fack07/OmegaSumo/firmware/Core/Src/main.c

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
/* Includes ------------------------------------------------------------------*/
#include "main.h"

/* USER CODE BEGIN Includes */
#include "stm32f4xx.h"
#include "system_stm32f4xx.h"
/* USER CODE END Includes */

TIM_HandleTypeDef htim1;
TIM_HandleTypeDef htim2;
TIM_HandleTypeDef htim4;
TIM_HandleTypeDef htim11;

/* USER CODE BEGIN PV */


#define NTRANS 27884	// Número de Transições
#define NESTADOS 2864	// Número de Estados
#define BUFFER 10	// Máximo Número de Eventos no Buffer

const unsigned int event[NTRANS]={0,4,7,8,9,11,13,15,17,18,19,0,1,4,7,8,9,11,13,15,17,18,19,8,9,11,13,15,16,17,18,19,1,8,9,11,13,15,16,17,18,19,8,9,11,13,15,16,17,18,19,
		1,8,9,11,13,15,16,17,18,19,0,4,7,8,9,11,13,15,17,18,19,22,0,1,4,7,8,9,11,13,15,17,18,19,22,8,9,11,13,15,17,18,19,22,1,8,9,11,13,15,17,
		18,19,22,8,9,11,13,15,17,18,19,22,1,8,9,11,13,15,17,18,19,22,8,9,11,13,15,17,18,19,22,1,8,9,11,13,15,17,18,19,22,8,9,11,13,15,17,18,19,22,1,
		8,9,11,13,15,17,18,19,22,2,4,7,8,9,11,14,15,17,18,19,4,7,8,9,11,14,15,17,18,19,1,2,4,7,8,9,11,14,15,17,18,19,1,4,7,8,9,11,14,15,17,
		18,19,8,9,11,14,15,16,17,18,19,1,8,9,11,14,15,16,17,18,19,8,9,11,14,15,16,17,18,19,1,8,9,11,14,15,16,17,18,19,2,4,7,8,9,11,14,15,17,18,19,
		22,4,7,8,9,11,14,15,17,18,19,22,1,2,4,7,8,9,11,14,15,17,18,19,22,1,4,7,8,9,11,14,15,17,18,19,22,8,9,11,14,15,17,18,19,22,1,8,9,11,14,
		15,17,18,19,22,8,9,11,14,15,17,18,19,22,1,8,9,11,14,15,17,18,19,22,8,9,11,14,15,17,18,19,22,1,8,9,11,14,15,17,18,19,22,8,9,11,14,15,17,18,19,
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
		2040,2041,0,2043,2044,2045,2046,2047,2048,2049,2050,0,2052,2053,2054,2055,2056,2057,2058,2059,2060,0,2062,2063,2064,2065,2066,2067,2068,2069,0,2071,2072,2073,2074,2075,2076,2077,2078,2079,0,2081,2082,2083,2084,2085,2086,2087,2088,2089,0,
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

/* USER CODE END PV */

void SystemClock_Config(void);
static void MX_GPIO_Init(void);
static void MX_TIM4_Init(void);
static void MX_TIM11_Init(void);
static void MX_TIM1_Init(void);
static void MX_TIM2_Init(void);
/* USER CODE BEGIN 0 */
// Mapeamento de eventos não controláveis como entradas
#define p1a 8	// Entrada 0
#define p2a 9	// Entrada 1
#define p2p 10	// Entrada 2
#define p3a 11	// Entrada 3
#define p3p 12	// Entrada 4
#define p4a 13	// Entrada 5
#define p4p 14	// Entrada 6
#define p5a 15	// Entrada 7
#define s1 17	// Entrada 8
#define s2 18	// Entrada 9
#define s3 19	// Entrada 10

// Mapeamento de eventos controláveis
#define frente 0
#define frenteDefesa 1
#define gd 2
#define gd90 3
#define gdataque 4
#define ge 5
#define ge90 6
#define geataque 7
#define re 16
#define tg90 20
#define tgataque 21
#define tre 22
#define turbo 23

// Definição dos eventos de saída

#define MOTOR_E_ON  HAL_GPIO_WritePin(MOTOR_E_ENABLE_GPIO_Port, MOTOR_E_ENABLE_Pin, GPIO_PIN_SET)
#define MOTOR_E_OFF HAL_GPIO_WritePin(MOTOR_E_ENABLE_GPIO_Port, MOTOR_E_ENABLE_Pin, GPIO_PIN_RESET)
#define MOTOR_D_ON  HAL_GPIO_WritePin(MOTOR_D_ENABLE_GPIO_Port, MOTOR_D_ENABLE_Pin, GPIO_PIN_SET)
#define MOTOR_D_OFF HAL_GPIO_WritePin(MOTOR_D_ENABLE_GPIO_Port, MOTOR_D_ENABLE_Pin, GPIO_PIN_RESET)
#define LED1_ON  HAL_GPIO_WritePin(GPIOE, LED1_Pin, GPIO_PIN_SET)
#define LED1_OFF HAL_GPIO_WritePin(GPIOE, LED1_Pin, GPIO_PIN_RESET)
#define LED2_ON  HAL_GPIO_WritePin(GPIOE, LED2_Pin, GPIO_PIN_SET)
#define LED2_OFF HAL_GPIO_WritePin(GPIOE, LED2_Pin, GPIO_PIN_RESET)
#define LED3_ON  HAL_GPIO_WritePin(GPIOE, LED3_Pin, GPIO_PIN_SET)
#define LED3_OFF HAL_GPIO_WritePin(GPIOE, LED3_Pin, GPIO_PIN_RESET)
#define LED4_ON  HAL_GPIO_WritePin(GPIOC, LED4_Pin, GPIO_PIN_SET)
#define LED4_OFF HAL_GPIO_WritePin(GPIOC, LED4_Pin, GPIO_PIN_RESET)
#define LED5_ON  HAL_GPIO_WritePin(GPIOC, LED5_Pin, GPIO_PIN_SET)
#define LED5_OFF HAL_GPIO_WritePin(GPIOC, LED5_Pin, GPIO_PIN_RESET)
#define LED6_ON  HAL_GPIO_WritePin(GPIOA, LED6_Pin, GPIO_PIN_SET)
#define LED6_OFF HAL_GPIO_WritePin(GPIOA, LED6_Pin, GPIO_PIN_RESET)
#define LED7_ON  HAL_GPIO_WritePin(GPIOA, LED7_Pin, GPIO_PIN_SET)
#define LED7_OFF HAL_GPIO_WritePin(GPIOA, LED7_Pin, GPIO_PIN_RESET)
#define LED8_ON  HAL_GPIO_WritePin(GPIOA, LED8_Pin, GPIO_PIN_SET)
#define LED8_OFF HAL_GPIO_WritePin(GPIOA, LED8_Pin, GPIO_PIN_RESET)

//váriaveis de velocidade

uint16_t v_frente=350; //velocidade frente 251~475
uint16_t v_re=100; // velocidade re 249~5
uint16_t v_eixo1=350; //velocidade roda para frente
uint16_t v_eixo2=100; //velocidade roda para trás
uint16_t v_girar=350;
uint16_t v_turbo=380; //velocidade max 475



void andar(void);
void andar_re(void);
void esquerda_eixo(void);
void direita_eixo(void);
void esquerda(void);
void direita(void);
void andar_turbo(void);
void parar(void);

void Temporizador_ms(unsigned int);		//Configura Timer

//Declaração de variáveis globais
unsigned char buffer[BUFFER];		//Buffer para armazenar a fila de enventos externos
unsigned char n_buffer=0;		//Número de eventos no Buffer
int occur_event=-1;
int current_state = 0;
int led=250;
unsigned char bandeira=0;

/* USER CODE END 0 */

/**
  * @brief  The application entry point.
  * @retval int
  */
int main(void)
{
  /* MCU Configuration--------------------------------------------------------*/

  /* Reset of all peripherals, Initializes the Flash interface and the Systick. */
  HAL_Init();

  /* Configure the system clock */
  SystemClock_Config();

  /* Initialize all configured peripherals */
  MX_GPIO_Init();
  MX_TIM4_Init();
  MX_TIM11_Init();
  MX_TIM1_Init();
  MX_TIM2_Init();
  /* USER CODE BEGIN 2 */


	unsigned int k;
				//Evento ocorrido
	//Estado atual inicializado com estado inicial
	char g=0; 			//Flag para gerador aleatório de eventos
	char gerar_evento=1;			//Flag para habilitar a temporização de eventos controláveis
	char mealy_output = 0;		//Inicializa saída periférica
	unsigned char iniciar=0;
	HAL_TIM_PWM_Start(&htim4, TIM_CHANNEL_2);
	HAL_TIM_PWM_Start(&htim11, TIM_CHANNEL_1);



  /* USER CODE END 2 */

  /* Infinite loop */
  /* USER CODE BEGIN WHILE */
  while (1)
  {
    /* USER CODE END WHILE */

    /* USER CODE BEGIN 3 */

	  if(HAL_GPIO_ReadPin(MICROSTART_GPIO_Port, MICROSTART_Pin)==GPIO_PIN_SET && iniciar==0){
		  HAL_TIM_Base_Start_IT(&htim2);
		  HAL_GPIO_WritePin(MOTOR_D_ENABLE_GPIO_Port, MOTOR_D_ENABLE_Pin, GPIO_PIN_SET);
		  HAL_GPIO_WritePin(MOTOR_E_ENABLE_GPIO_Port, MOTOR_E_ENABLE_Pin, GPIO_PIN_SET);

		  iniciar=1;
		  n_buffer=0;
	  }else if(HAL_GPIO_ReadPin(MICROSTART_GPIO_Port, MICROSTART_Pin)==GPIO_PIN_RESET && iniciar==1){

	  		  HAL_GPIO_WritePin(MOTOR_D_ENABLE_GPIO_Port, MOTOR_D_ENABLE_Pin, GPIO_PIN_RESET);
	  		  HAL_GPIO_WritePin(MOTOR_E_ENABLE_GPIO_Port, MOTOR_E_ENABLE_Pin, GPIO_PIN_RESET);
	  }

	  if(n_buffer == 0)//se não existir evento no buffer então gerar um evento interno(evento controlável)
		{
			if(__HAL_TIM_GET_FLAG(&htim1, TIM_FLAG_UPDATE) != RESET)	//Se o timer estourar, habilita a geração de eventos
			{
				gerar_evento=1;
			}
			if(gerar_evento==1)
			{
				switch(g)	//Aqui é implementado um gerador automático de eventos controláveis
				{
				case(0):
					occur_event=frente;
					g++;
					break;
				case(1):
					occur_event=frenteDefesa;
					g++;
					break;
				case(2):
					occur_event=gd;
					g++;
					break;
				case(3):
					occur_event=gd90;
					g++;
					break;
				case(4):
					occur_event=gdataque;
					g++;
					break;
				case(5):
					occur_event=ge;
					g++;
					break;
				case(6):
					occur_event=ge90;
					g++;
					break;
				case(7):
					occur_event=geataque;
					g++;
					break;
				case(8):
					occur_event=re;
					g++;
					break;
				case(9):
					occur_event=tg90;
					g++;
					break;
				case(10):
					occur_event=tgataque;
					g++;
					break;
				case(11):
					occur_event=tre;
					g++;
					break;
				case(12):
					occur_event=turbo;
					g=0;
					break;
				}
			}
		}

		else 	//se existir evento não controlável pegar do buffer
		{
			occur_event = buffer[0];
			n_buffer--;
			k = 0;
			while(k<n_buffer)
			{
				buffer[k] = buffer[k+1];
				k+=1;
			}
		}



		//Jogador de autômato
		k = rfirst[current_state];
		if(k==0)
		{
			return;     //Dead Lock!!!
		}
		else
		{
			while(k>0)
			{
				k-=1;
				if(event[k] == occur_event)
				{
					current_state = in_state[k];
					mealy_output = 1;
					break;
				}
				k = rnext[k];
			}
		}

		if(mealy_output) //Se o evento ocorrido for válido, então imprimir saída física
		{
			switch(occur_event)
			{
				//eventos controláveis
				case(frente):	//Adicionar Ação para o Evento frente;
					andar();
					LED1_ON;
					LED2_OFF;
					LED3_OFF;
					LED4_OFF;
					LED5_OFF;
					LED6_OFF;
					LED7_OFF;
					LED8_OFF;
					break;
				case(frenteDefesa):	//Adicionar Ação para o Evento frenteDefesa;
					andar_turbo();
					LED1_ON;
					LED2_OFF;
					LED3_OFF;
					LED4_OFF;
					LED5_OFF;
					LED6_OFF;
					LED7_OFF;
					LED8_OFF;
					break;
				case(gd):	//Adicionar Ação para o Evento gd;
					direita();
					LED1_OFF;
					LED2_OFF;
					LED3_ON;
					LED4_ON;
					LED5_OFF;
					LED6_OFF;
					LED7_OFF;
					LED8_OFF;
					break;
				case(gd90):	//Adicionar Ação para o Evento gd90;
					direita_eixo();
					LED1_OFF;
					LED2_OFF;
					LED3_OFF;
					LED4_OFF;
					LED5_ON;
					LED6_ON;
					LED7_ON;
					LED8_ON;
					Temporizador_ms(500);
					gerar_evento=0;
					break;
				case(ge):	//Adicionar Ação para o Evento ge;
					esquerda();
					LED1_OFF;
					LED2_OFF;
					LED3_OFF;
					LED4_OFF;
					LED5_ON;
					LED6_ON;
					LED7_OFF;
					LED8_OFF;
					break;
				case(ge90):	//Adicionar Ação para o Evento ge90;
					esquerda_eixo();
					LED1_ON;
					LED2_ON;
					LED3_ON;
					LED4_ON;
					LED5_OFF;
					LED6_OFF;
					LED7_OFF;
					LED8_OFF;
					Temporizador_ms(500);
					gerar_evento=0;
					break;
				case(re):	//Adicionar Ação para o Evento re;
					andar_re();
					LED1_OFF;
					LED2_OFF;
					LED3_OFF;
					LED4_OFF;
					LED5_OFF;
					LED6_OFF;
					LED7_OFF;
					LED8_ON;
					Temporizador_ms(500);
					gerar_evento=0;
					break;
				case(tg90):	//Adicionar Ação para o Evento tg90;

					break;
				case(tre):	//Adicionar Ação para o Evento tre;

					break;
				case(turbo):	//Adicionar Ação para o Evento turbo;
					andar_turbo();
					LED1_ON;
					LED2_ON;
					LED3_ON;
					LED4_ON;
					LED5_ON;
					LED6_ON;
					LED7_ON;
					LED8_ON;
					break;
				case(gdataque):	//Adicionar Ação para o Evento gdataque;
					LED1_OFF;
					LED2_OFF;
					LED3_OFF;
					LED4_OFF;
					LED5_ON;
					LED6_ON;
					LED7_ON;
					LED8_ON;
					direita_eixo();
					Temporizador_ms(500);
					gerar_evento=0;
					break;
				case(geataque):	//Adicionar Ação para o Evento geataque;
					LED1_ON;
					LED2_ON;
					LED3_ON;
					LED4_ON;
					LED5_OFF;
					LED6_OFF;
					LED7_OFF;
					LED8_OFF;
					esquerda_eixo();
					Temporizador_ms(500);
					gerar_evento=0;
					break;
				case(tgataque):	//Adicionar Ação para o Evento tgataque;

					break;
				//eventos não controláveis
				case(p1a):	//Adicionar Ação para o Evento p1a;

					gerar_evento=1;
					break;
				case(p2a):	//Adicionar Ação para o Evento p2a;

					gerar_evento=1;
					break;
				case(p2p):	//Adicionar Ação para o Evento p2p;

					gerar_evento=0;
					break;
				case(p3a):	//Adicionar Ação para o Evento p3a;

					gerar_evento=1;
					break;
				case(p3p):	//Adicionar Ação para o Evento p3p;

					gerar_evento=0;
					break;
				case(p4a):	//Adicionar Ação para o Evento p4a;

					gerar_evento=1;
					break;
				case(p4p):	//Adicionar Ação para o Evento p4p;

					gerar_evento=0;
					break;
				case(p5a):	//Adicionar Ação para o Evento p5a;

					gerar_evento=1;
					break;
				case(s1):	//Adicionar Ação para o Evento s1;

					gerar_evento=1;
					break;
				case(s2):	//Adicionar Ação para o Evento s2;

					gerar_evento=1;
					break;
				case(s3):	//Adicionar Ação para o Evento s3;

					gerar_evento=1;
					break;
			}//fim switch
			mealy_output = 0;
			occur_event = -1;
		}//fim if(mealy_output)
  }
  /* USER CODE END 3 */
}

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
/* USER CODE BEGIN 4 */

void andar(void){
	  __HAL_TIM_SET_COMPARE(&htim11, TIM_CHANNEL_1,v_frente);
	  __HAL_TIM_SET_COMPARE(&htim4, TIM_CHANNEL_2,v_frente);
}
void andar_re(void){
	  __HAL_TIM_SET_COMPARE(&htim11, TIM_CHANNEL_1,v_re);
	  __HAL_TIM_SET_COMPARE(&htim4, TIM_CHANNEL_2,v_re);
}
void esquerda_eixo(void){
	  __HAL_TIM_SET_COMPARE(&htim11, TIM_CHANNEL_1,v_eixo1);
	  __HAL_TIM_SET_COMPARE(&htim4, TIM_CHANNEL_2,v_eixo2);
}
void direita_eixo(void){
	  __HAL_TIM_SET_COMPARE(&htim11, TIM_CHANNEL_1,v_eixo2);
	  __HAL_TIM_SET_COMPARE(&htim4, TIM_CHANNEL_2,v_eixo1);
}
void esquerda(void){
	  __HAL_TIM_SET_COMPARE(&htim11, TIM_CHANNEL_1,v_girar);
	  __HAL_TIM_SET_COMPARE(&htim4, TIM_CHANNEL_2,250);
}
void direita(void){
	  __HAL_TIM_SET_COMPARE(&htim11, TIM_CHANNEL_1,250);
	  __HAL_TIM_SET_COMPARE(&htim4, TIM_CHANNEL_2,v_girar);
}
void andar_turbo(void){
	  __HAL_TIM_SET_COMPARE(&htim11, TIM_CHANNEL_1,v_turbo);
	  __HAL_TIM_SET_COMPARE(&htim4, TIM_CHANNEL_2,v_turbo);
}
void parar(void){
	  HAL_TIM_PWM_Stop(&htim4, TIM_CHANNEL_2);
	  HAL_TIM_PWM_Stop(&htim11, TIM_CHANNEL_1);
}

void HAL_GPIO_EXTI_Callback(uint16_t GPIO_Pin)
{
  if(GPIO_Pin == PRESENCA1_Pin) {
	if(HAL_GPIO_ReadPin(PRESENCA1_GPIO_Port, PRESENCA1_Pin) == GPIO_PIN_SET)
	{
		buffer[n_buffer]=p1a;	//Atribuir evento a GPIOC_Pin_0
		if(n_buffer<BUFFER-1) n_buffer++;
	}
  }else if(GPIO_Pin == PRESENCA2_Pin) {
	if(HAL_GPIO_ReadPin(PRESENCA2_GPIO_Port, PRESENCA2_Pin) == GPIO_PIN_SET)
	{
		buffer[n_buffer]=p2a;	//Atribuir evento a GPIOC_Pin_0
		if(n_buffer<BUFFER-1) n_buffer++;
	}else{
		buffer[n_buffer]=p2p;	//Atribuir evento a GPIOC_Pin_0
		if(n_buffer<BUFFER-1) n_buffer++;
	}
  }else if(GPIO_Pin == PRESENCA3_Pin) {
	if(HAL_GPIO_ReadPin(PRESENCA3_GPIO_Port, PRESENCA3_Pin) == GPIO_PIN_SET)
	{
		buffer[n_buffer]=p3a;	//Atribuir evento a GPIOC_Pin_0
		if(n_buffer<BUFFER-1) n_buffer++;
	}else{
		buffer[n_buffer]=p3p;	//Atribuir evento a GPIOC_Pin_0
		if(n_buffer<BUFFER-1) n_buffer++;
	}
  }else if(GPIO_Pin == PRESENCA4_Pin) {
	if(HAL_GPIO_ReadPin(PRESENCA4_GPIO_Port, PRESENCA4_Pin) == GPIO_PIN_SET)
	{
		buffer[n_buffer]=p4a;	//Atribuir evento a GPIOC_Pin_0
		if(n_buffer<BUFFER-1) n_buffer++;
	}else{
		buffer[n_buffer]=p4p;	//Atribuir evento a GPIOC_Pin_0
		if(n_buffer<BUFFER-1) n_buffer++;
	}
  }else if(GPIO_Pin == PRESENCA5_Pin) {
	if(HAL_GPIO_ReadPin(PRESENCA5_GPIO_Port, PRESENCA5_Pin) == GPIO_PIN_SET)
	{
		buffer[n_buffer]=p5a;	//Atribuir evento a GPIOC_Pin_0
		if(n_buffer<BUFFER-1) n_buffer++;
	}
  }else if(GPIO_Pin == FAIXA1_Pin) {
	if(HAL_GPIO_ReadPin(FAIXA1_GPIO_Port, FAIXA1_Pin) == GPIO_PIN_SET)
	{
		buffer[n_buffer]=s1;	//Atribuir evento a GPIOC_Pin_0
		if(n_buffer<BUFFER-1) n_buffer++;
	}

  }else if(GPIO_Pin == FAIXA2_Pin) {
		if(HAL_GPIO_ReadPin(FAIXA2_GPIO_Port, FAIXA2_Pin) == GPIO_PIN_SET)
		{
			buffer[n_buffer]=s2;	//Atribuir evento a GPIOC_Pin_0
			if(n_buffer<BUFFER-1) n_buffer++;
		}

  }else if(GPIO_Pin == FAIXA3_Pin) {
	if(HAL_GPIO_ReadPin(FAIXA3_GPIO_Port, FAIXA3_Pin) == GPIO_PIN_SET)
	{
		buffer[n_buffer]=s3;	//Atribuir evento a GPIOC_Pin_0
		if(n_buffer<BUFFER-1) n_buffer++;
	}
  }
}

void HAL_TIM_PeriodElapsedCallback(TIM_HandleTypeDef *htim) {
    if (htim->Instance == TIM2) {
    	if(bandeira==0){
    		HAL_GPIO_WritePin(BANDEIRA_GPIO_Port, BANDEIRA_Pin, GPIO_PIN_SET);
    		bandeira=1;
    	}else{
    		HAL_GPIO_WritePin(BANDEIRA_GPIO_Port, BANDEIRA_Pin, GPIO_PIN_RESET); // Desliga o motor
    		HAL_TIM_Base_Stop_IT(&htim2); // Para o timer
    	}
//    	HAL_GPIO_WritePin(BANDEIRA_GPIO_Port, BANDEIRA_Pin, GPIO_PIN_RESET); // Desliga o motor
//    	HAL_TIM_Base_Stop_IT(&htim2); // Para o timer
    }
}
//void EXTI0_IRQHandler(void)
//{
//	HAL_GPIO_EXTI_IRQHandler(PRESENCA4_Pin);
//}
//
//void EXTI3_IRQHandler(void) //
//{
//	HAL_GPIO_EXTI_IRQHandler(PRESENCA5_Pin);
//}
//
//void EXTI9_5_IRQHandler(void) //
//{
//	if(__HAL_GPIO_EXTI_GET_IT(PRESENCA1_Pin!=RESET)){
//		HAL_GPIO_EXTI_IRQHandler(PRESENCA1_Pin);
//	}else if(__HAL_GPIO_EXTI_GET_IT(PRESENCA3_Pin!=RESET)){
//		HAL_GPIO_EXTI_IRQHandler(PRESENCA3_Pin);
//	}else if(__HAL_GPIO_EXTI_GET_IT(PRESENCA2_Pin!=RESET)){
//		HAL_GPIO_EXTI_IRQHandler(PRESENCA2_Pin);
//	}
//}
//
//void EXTI15_10_IRQHandler(void) //
//{
//	if(__HAL_GPIO_EXTI_GET_IT(FAIXA2_Pin!=RESET)){
//		HAL_GPIO_EXTI_IRQHandler(FAIXA2_Pin);
//	}else if(__HAL_GPIO_EXTI_GET_IT(FAIXA3_Pin!=RESET)){
//		HAL_GPIO_EXTI_IRQHandler(FAIXA3_Pin);
//	}else if(__HAL_GPIO_EXTI_GET_IT(FAIXA1_Pin)){
//		HAL_GPIO_EXTI_IRQHandler(FAIXA1_Pin);
//	}
//}

void Temporizador_ms(unsigned int TEMPO)
{
	__HAL_TIM_CLEAR_IT(&htim1, TIM_IT_UPDATE);
	__HAL_TIM_SET_AUTORELOAD(&htim1, TEMPO*5);
	HAL_TIM_Base_Start_IT(&htim1);
}


/* USER CODE END 4 */
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
